3zuli/mprojbot/hw/mprojbot_schematic/mprojbot_schematic.kicad_pcb

## KiCad design schematics/ALDIS/ALDIS.sch

Schematic: ALDIS.sch

Parts:
A1: Arduino_Nano_v3.x; Arduino_Nano
D1: LED_BGCR
J1: Conn_01x04_Male
R1, R2: 150
R3: 220
SW1: SW_Push

Notes on the sheet:
+5V
GND
ALDIS - Main Schematic
